mlab-modules/ACOMP01/doc/gen/dxf/ACOMP01-Edge_Cuts.dxf

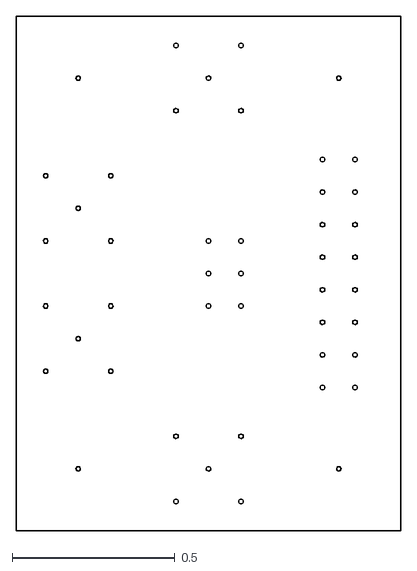
[picture p12: CAD file, 2026-01-18]
doc/gen/dxf/ACOMP01-Edge_Cuts.dxf
1.18 x 1.58
